mrstefangrimm/SmartCardChanger/Software/src/scc/public/SCC-VirmsGroupRotatorWhite.obj

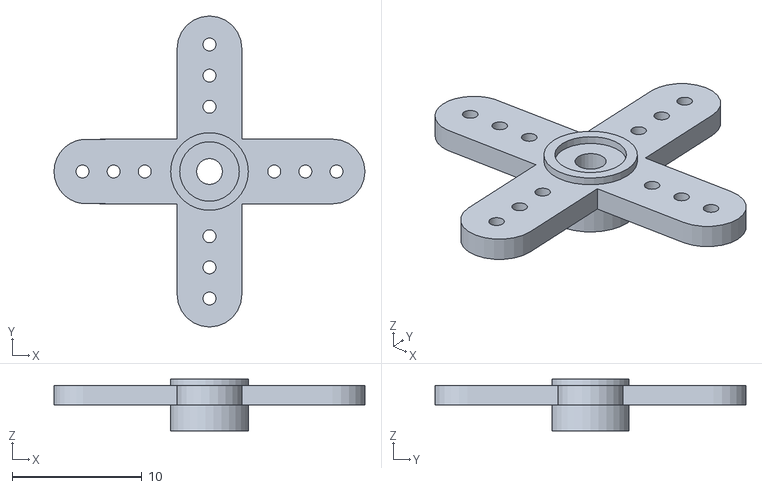
[picture p16: CAD file, 2025-10-20]
Software/src/scc/public/SCC-VirmsGroupRotatorWhite.obj
24.0 x 24.0 x 4.00
