mrstefangrimm/SmartCardChanger/Software/src/scc/public/SCC-VirmsGroupCarriageTransparent.obj

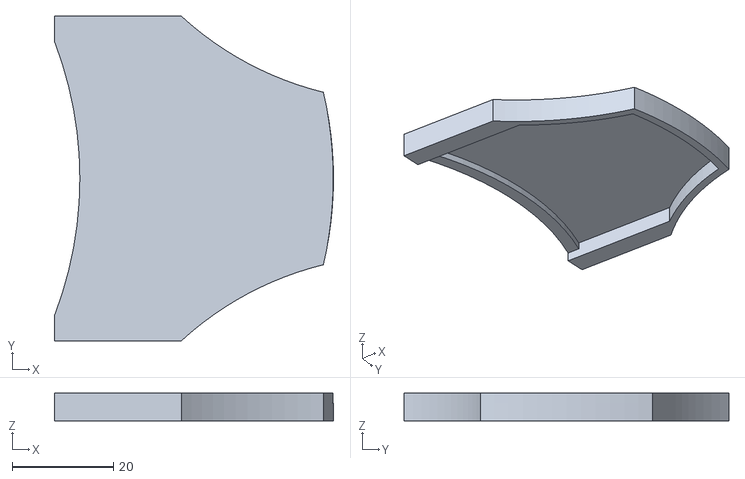
[picture p17: CAD file, 2025-10-20]
Software/src/scc/public/SCC-VirmsGroupCarriageTransparent.obj
55.0 x 64.0 x 5.50
