mrstefangrimm/SmartCardChanger/Software/src/scc/public/SCC-VirmsGroupCarriageWood.obj

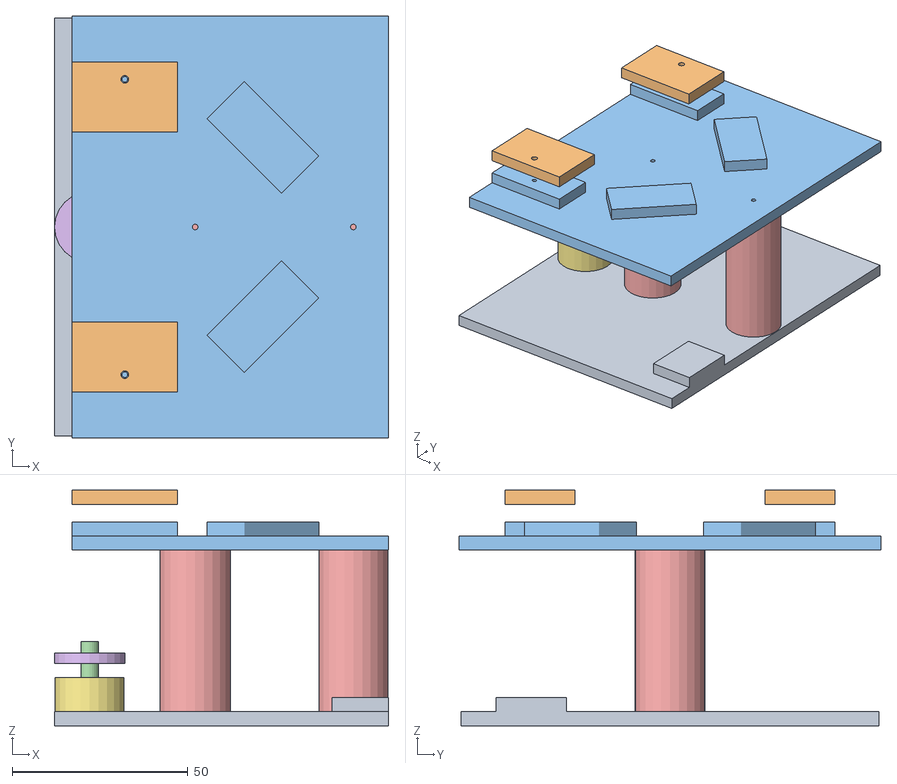
[picture p18: CAD file, 2025-10-20]
Software/src/scc/public/SCC-VirmsGroupCarriageWood.obj
95.0 x 120.0 x 67.0
SCC_Carriage_Reader_Lid_Wood1
SCC_Carriage_Reader_Platform1
SCC_Carriage_Slider_Bolt1
SCC_Carriage_Slider_Feet_1_1
SCC_Carriage_Slider_Fixation1
SCC_Carriage_Slider_Spacer1
