mrstefangrimm/SmartCardChanger/Software/src/scc/public/SCC-VirmsGroupCarriageGreen.obj

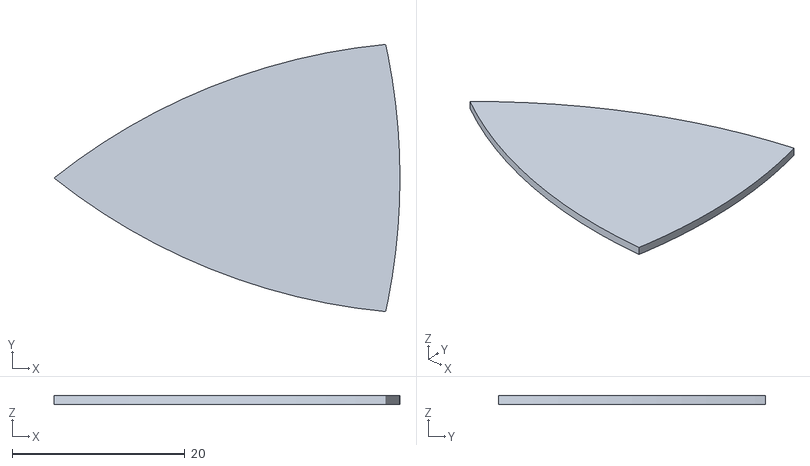
[picture p19: CAD file, 2025-10-20]
Software/src/scc/public/SCC-VirmsGroupCarriageGreen.obj
40.0 x 30.9 x 1.00
