mrstefangrimm/SmartCardChanger/Software/src/scc/public/SCC-VirmsGroupRotatorCardboard.obj

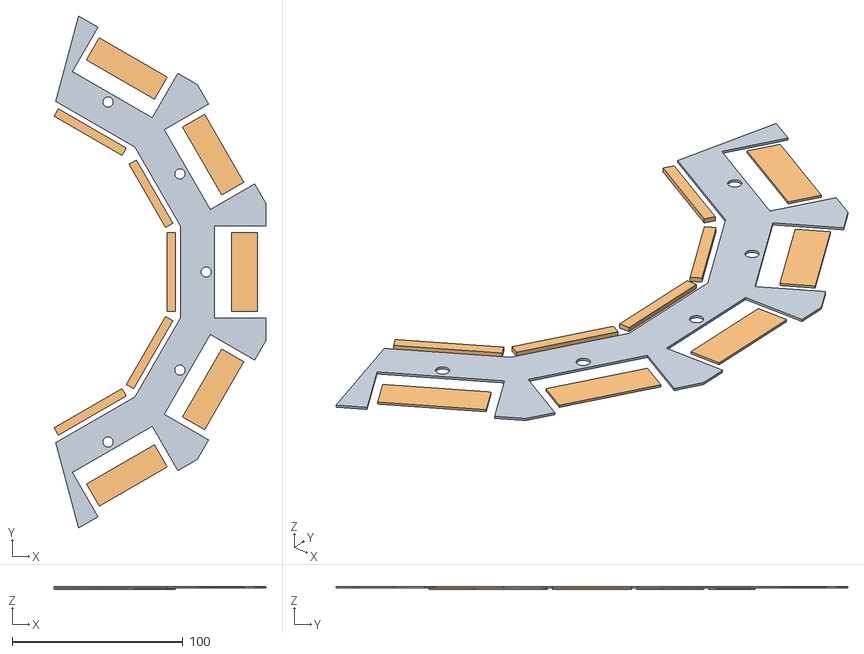
[picture p20: CAD file, 2025-10-20]
Software/src/scc/public/SCC-VirmsGroupRotatorCardboard.obj
124.1 x 300.0 x 2.00
SCC_Rotatator_Cardboard1
SCC_Rotatator_Lid_Cardboard1
